firstyearstudent/Energy_Meter/Energy_Meter.recovered.2026-06-18_162926.pdf

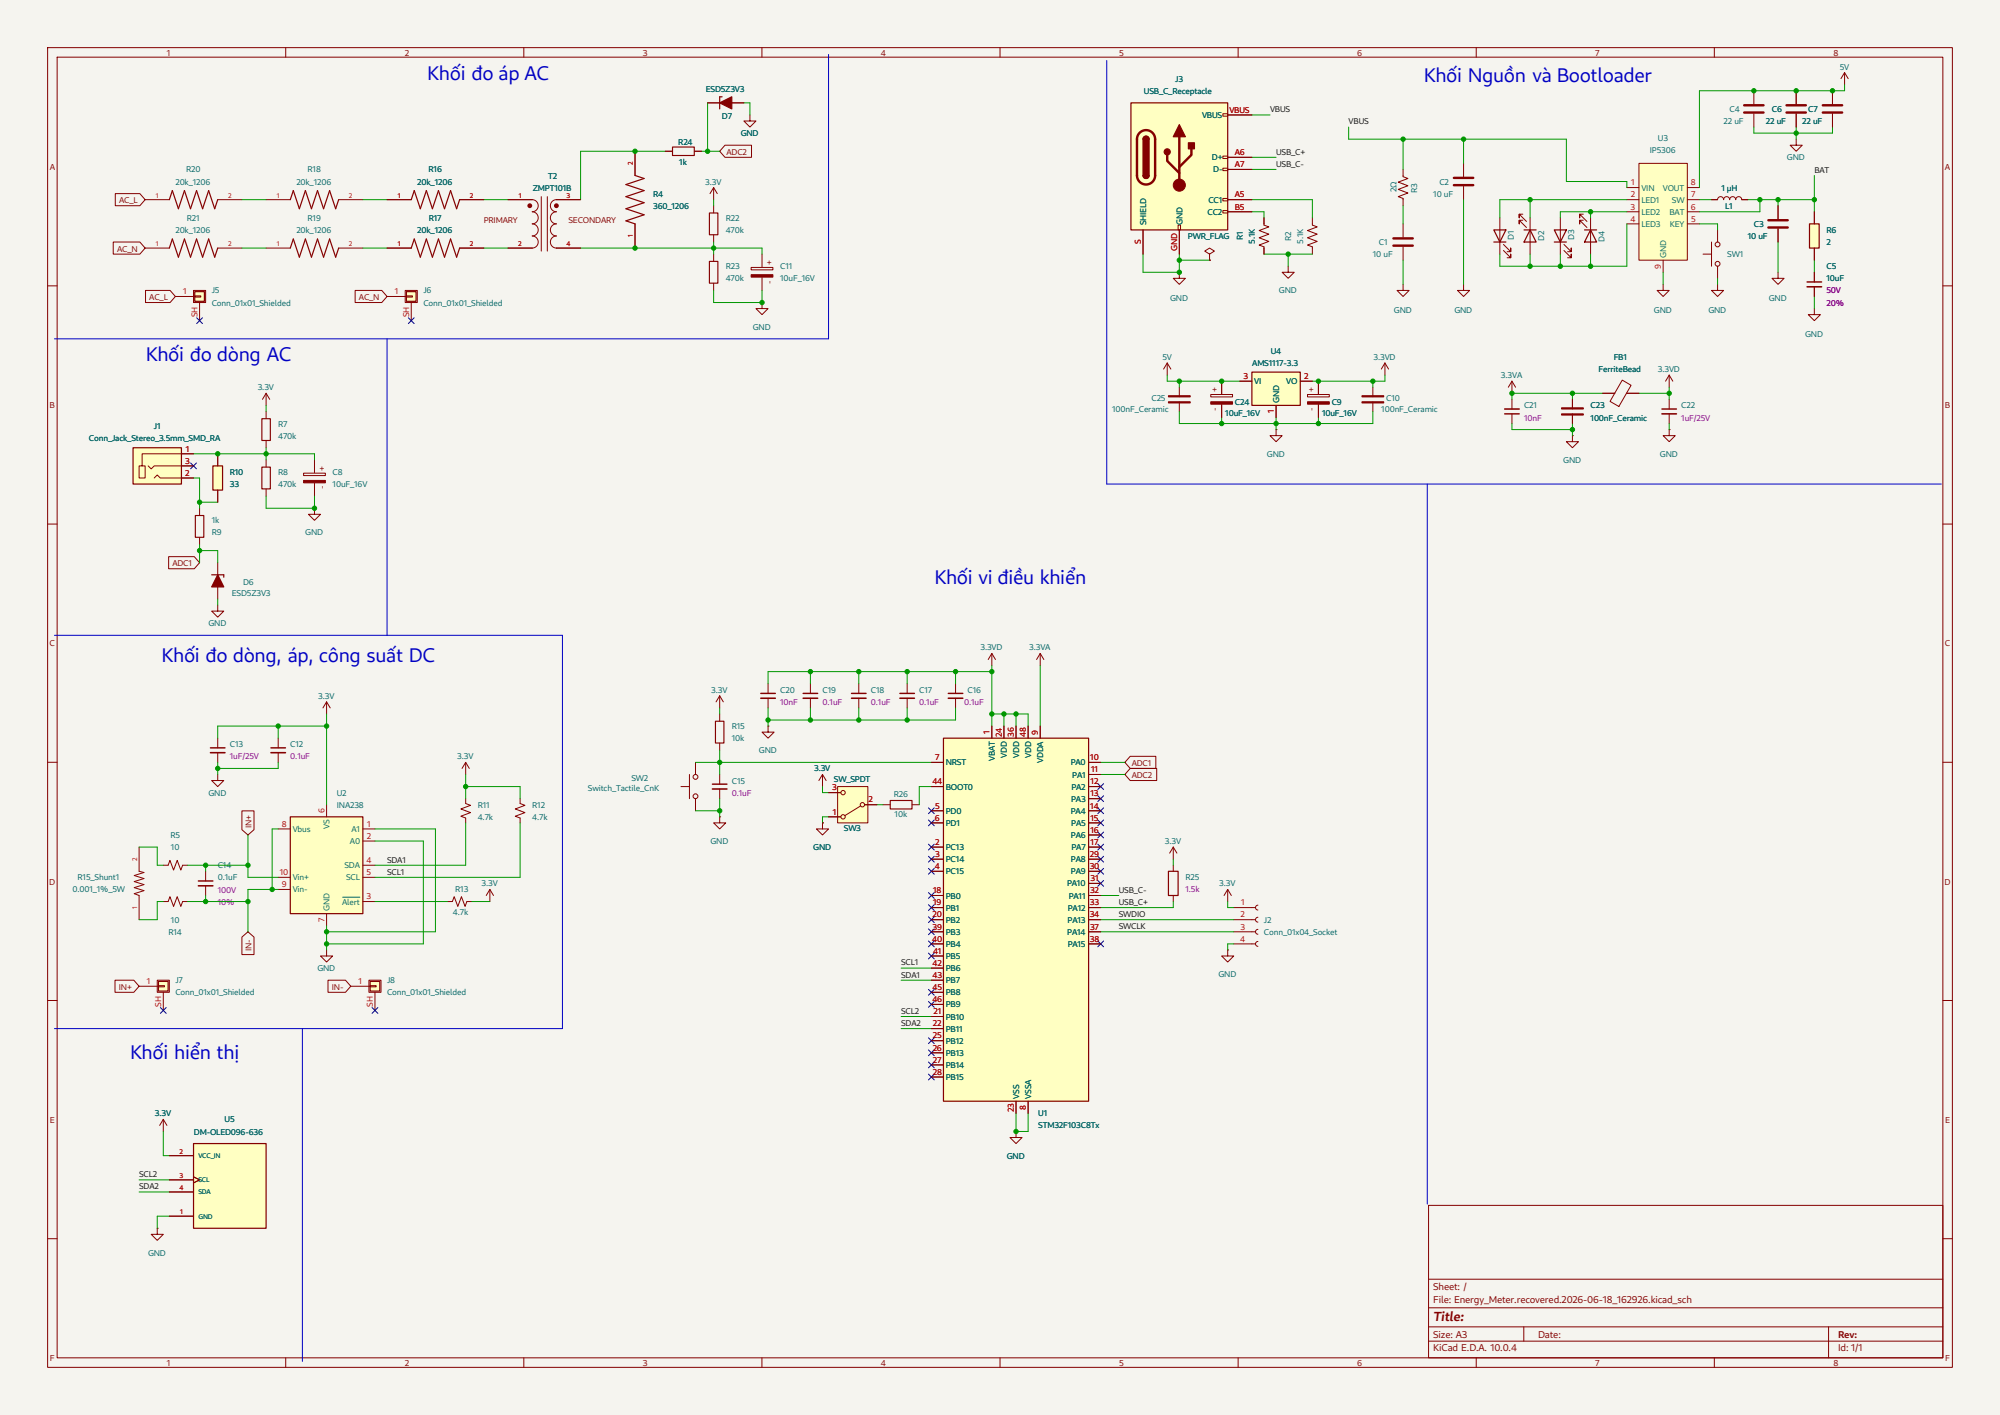
[picture p4: page 1]

Khối đo áp AC

Khối Nguồn và Bootloader

Khối đo dòng AC

1 VO 2 VI 3 U4 AMS1117-3.3 GND GND

Khối vi điều khiển
U1 STM32F103C8Tx VBAT

Khối đo dòng, áp, công suất DC
